mattlokes/zwallremote/firmware/src/zcl_samplesw_data.c

/**************************************************************************************************
  Filename:       zcl_samplesw_data.c
  Revised:        $Date: 2014-07-30 12:57:37 -0700 (Wed, 30 Jul 2014) $
  Revision:       $Revision: 39591 $


  Description:    Zigbee Cluster Library - sample device application.


  Copyright 2006-2014 Texas Instruments Incorporated. All rights reserved.

  IMPORTANT: Your use of this Software is limited to those specific rights
  granted under the terms of a software license agreement between the user
  who downloaded the software, his/her employer (which must be your employer)
  and Texas Instruments Incorporated (the "License").  You may not use this
  Software unless you agree to abide by the terms of the License. The License
  limits your use, and you acknowledge, that the Software may not be modified,
  copied or distributed unless embedded on a Texas Instruments microcontroller
  or used solely and exclusively in conjunction with a Texas Instruments radio
  frequency transceiver, which is integrated into your product.  Other than for
  the foregoing purpose, you may not use, reproduce, copy, prepare derivative
  works of, modify, distribute, perform, display or sell this Software and/or
  its documentation for any purpose.

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
  Should you have any questions regarding your right to use this Software,
  contact Texas Instruments Incorporated at www.TI.com.
**************************************************************************************************/

/*********************************************************************
 * INCLUDES
 */
#include "ZComDef.h"
#include "OSAL.h"
#include "AF.h"
#include "ZDConfig.h"

#include "zcl.h"
#include "zcl_general.h"
#include "zcl_ha.h"
#include "zcl_poll_control.h"
#include "zcl_electrical_measurement.h"
#include "zcl_diagnostic.h"
#include "zcl_meter_identification.h"
#include "zcl_appliance_identification.h"
#include "zcl_appliance_events_alerts.h"
#include "zcl_power_profile.h"
#include "zcl_appliance_control.h"
#include "zcl_appliance_statistics.h"
#include "zcl_hvac.h"
#include "zcl_ezmode.h"

#include "zcl_samplesw.h"

/*********************************************************************
 * CONSTANTS
 */

#define SAMPLESW_DEVICE_VERSION     0
#define SAMPLESW_FLAGS              0

#define SAMPLESW_HWVERSION          0
#define SAMPLESW_ZCLVERSION         0

/*********************************************************************
 * TYPEDEFS
 */

/*********************************************************************
 * MACROS
 */

/*********************************************************************
 * GLOBAL VARIABLES
 */

// Basic Cluster
const uint8 zclSampleSw_HWRevision = SAMPLESW_HWVERSION;
const uint8 zclSampleSw_ZCLVersion = SAMPLESW_ZCLVERSION;
const uint8 zclSampleSw_ManufacturerName[] = { 16, 'M','a','t','t',' ','I','n','s','t','r','u','m','e','n','t','s' };
const uint8 zclSampleSw_ModelId[] = { 12, 'Z','W','a','l','l','R','e','m','o','t','e','0'};
const uint8 zclSampleSw_DateCode[] = { 16, '2','0','1','9','0','4','0','5',' ',' ',' ',' ',' ',' ',' ',' ' };
const uint8 zclSampleSw_PowerSource = POWER_SOURCE_BATTERY;

uint8 zclSampleSw_LocationDescription[17] = { 16, ' ',' ',' ',' ',' ',' ',' ',' ',' ',' ',' ',' ',' ',' ',' ',' ' };
uint8 zclSampleSw_PhysicalEnvironment = 0;
uint8 zclSampleSw_DeviceEnable = DEVICE_ENABLED;

// Identify Cluster
uint16 zclSampleSw_IdentifyTime = 0;

// On/Off Cluster
uint8  zclSampleSw_OnOff = LIGHT_OFF;

/*********************************************************************
 * ATTRIBUTE DEFINITIONS - Uses REAL cluster IDs
 */
CONST zclAttrRec_t zclSampleSw_Attrs[SAMPLESW_MAX_ATTRIBUTES] =
{
  // *** General Basic Cluster Attributes ***
  {
    ZCL_CLUSTER_ID_GEN_BASIC,             // Cluster IDs - defined in the foundation (ie. zcl.h)
    {  // Attribute record
      ATTRID_BASIC_HW_VERSION,            // Attribute ID - Found in Cluster Library header (ie. zcl_general.h)
      ZCL_DATATYPE_UINT8,                 // Data Type - found in zcl.h
      ACCESS_CONTROL_READ,                // Variable access control - found in zcl.h
      (void *)&zclSampleSw_HWRevision  // Pointer to attribute variable
    }
  },
  {
    ZCL_CLUSTER_ID_GEN_BASIC,
    { // Attribute record
      ATTRID_BASIC_ZCL_VERSION,
      ZCL_DATATYPE_UINT8,
      ACCESS_CONTROL_READ,
      (void *)&zclSampleSw_ZCLVersion
    }
  },
  {
    ZCL_CLUSTER_ID_GEN_BASIC,
    { // Attribute record
      ATTRID_BASIC_MANUFACTURER_NAME,
      ZCL_DATATYPE_CHAR_STR,
      ACCESS_CONTROL_READ,
      (void *)zclSampleSw_ManufacturerName
    }
  },
  {
    ZCL_CLUSTER_ID_GEN_BASIC,
    { // Attribute record
      ATTRID_BASIC_MODEL_ID,
      ZCL_DATATYPE_CHAR_STR,
      ACCESS_CONTROL_READ,
      (void *)zclSampleSw_ModelId
    }
  },
  {
    ZCL_CLUSTER_ID_GEN_BASIC,
    { // Attribute record
      ATTRID_BASIC_DATE_CODE,
      ZCL_DATATYPE_CHAR_STR,
      ACCESS_CONTROL_READ,
      (void *)zclSampleSw_DateCode
    }
  },
  {
    ZCL_CLUSTER_ID_GEN_BASIC,
    { // Attribute record
      ATTRID_BASIC_POWER_SOURCE,
      ZCL_DATATYPE_UINT8,
      ACCESS_CONTROL_READ,
      (void *)&zclSampleSw_PowerSource
    }
  },
  {
    ZCL_CLUSTER_ID_GEN_BASIC,
    { // Attribute record
      ATTRID_BASIC_LOCATION_DESC,
      ZCL_DATATYPE_CHAR_STR,
      (ACCESS_CONTROL_READ | ACCESS_CONTROL_WRITE),
      (void *)zclSampleSw_LocationDescription
    }
  },
  {
    ZCL_CLUSTER_ID_GEN_BASIC,
    { // Attribute record
      ATTRID_BASIC_PHYSICAL_ENV,
      ZCL_DATATYPE_UINT8,
      (ACCESS_CONTROL_READ | ACCESS_CONTROL_WRITE),
      (void *)&zclSampleSw_PhysicalEnvironment
    }
  },
  {
    ZCL_CLUSTER_ID_GEN_BASIC,
    { // Attribute record
      ATTRID_BASIC_DEVICE_ENABLED,
      ZCL_DATATYPE_UINT8,
      (ACCESS_CONTROL_READ | ACCESS_CONTROL_WRITE),
      (void *)&zclSampleSw_DeviceEnable
    }
  },

  // *** Identify Cluster Attribute ***
  {
    ZCL_CLUSTER_ID_GEN_IDENTIFY,
    { // Attribute record
      ATTRID_IDENTIFY_TIME,
      ZCL_DATATYPE_UINT16,
      (ACCESS_CONTROL_READ | ACCESS_CONTROL_WRITE),
      (void *)&zclSampleSw_IdentifyTime
    }
  },

  // *** On / Off Cluster Attributes ***
  {
    ZCL_CLUSTER_ID_GEN_ON_OFF,
    { // Attribute record
      ATTRID_ON_OFF,
      ZCL_DATATYPE_BOOLEAN,
      ACCESS_CONTROL_READ,
      (void *)&zclSampleSw_OnOff
    }
  },

  // *** On / Off Switch Configuration Cluster *** //
  {
    ZCL_CLUSTER_ID_GEN_ON_OFF_SWITCH_CONFIG,
    { // Attribute record
      ATTRID_ON_OFF_SWITCH_TYPE,
      ZCL_DATATYPE_ENUM8,
      ACCESS_CONTROL_READ,
      (void *)&zclSampleSw_OnOffSwitchType
    }
  },
  {
    ZCL_CLUSTER_ID_GEN_ON_OFF_SWITCH_CONFIG,
    { // Attribute record
      ATTRID_ON_OFF_SWITCH_ACTIONS,
      ZCL_DATATYPE_ENUM8,
      ACCESS_CONTROL_READ | ACCESS_CONTROL_WRITE,
      (void *)&zclSampleSw_OnOffSwitchActions
    }
  },
};

/*********************************************************************
 * SIMPLE DESCRIPTOR
 */
// This is the Cluster ID List and should be filled with Application
// specific cluster IDs.
#define ZCLSAMPLESW_MAX_INCLUSTERS       2
const cId_t zclSampleSw_InClusterList[ZCLSAMPLESW_MAX_INCLUSTERS] =
{
  ZCL_CLUSTER_ID_GEN_BASIC,
  ZCL_CLUSTER_ID_GEN_IDENTIFY
};

const cId_t zclSampleSw_OutClusterList[] =
{
  ZCL_CLUSTER_ID_GEN_ON_OFF,
  ZCL_CLUSTER_ID_GEN_IDENTIFY,
#ifdef ZCL_LEVEL_CTRL
  ZCL_CLUSTER_ID_GEN_LEVEL_CONTROL,
#endif
  0
};

#define ZCLSAMPLESW_MAX_OUTCLUSTERS    ( ( sizeof( zclSampleSw_OutClusterList ) / sizeof( zclSampleSw_OutClusterList[0] ) ) - 1 )


SimpleDescriptionFormat_t zclSampleSw_SimpleDesc =
{
  SAMPLESW_ENDPOINT,                  //  int Endpoint;
  ZCL_HA_PROFILE_ID,                  //  uint16 AppProfId[2];
  ZCL_HA_DEVICEID_ON_OFF_SWITCH,      //  uint16 AppDeviceId[2];
  SAMPLESW_DEVICE_VERSION,            //  int   AppDevVer:4;
  SAMPLESW_FLAGS,                     //  int   AppFlags:4;
  ZCLSAMPLESW_MAX_INCLUSTERS,         //  byte  AppNumInClusters;
  (cId_t *)zclSampleSw_InClusterList, //  byte *pAppInClusterList;
  ZCLSAMPLESW_MAX_OUTCLUSTERS,        //  byte  AppNumInClusters;
  (cId_t *)zclSampleSw_OutClusterList //  byte *pAppInClusterList;
};

/*********************************************************************
 * GLOBAL FUNCTIONS
 */

/*********************************************************************
 * LOCAL FUNCTIONS
 */

/****************************************************************************
****************************************************************************/
